imchipwood/dumbpad/case/case v2/img/1.jpg

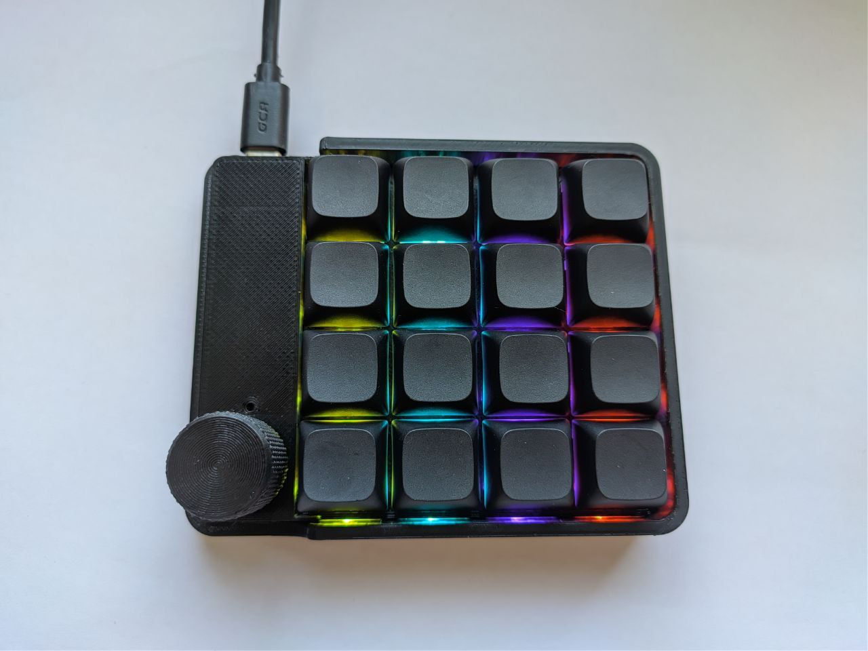
case/case v2/img/1.jpg
