imchipwood/dumbpad/case/case v2/img/2.jpg

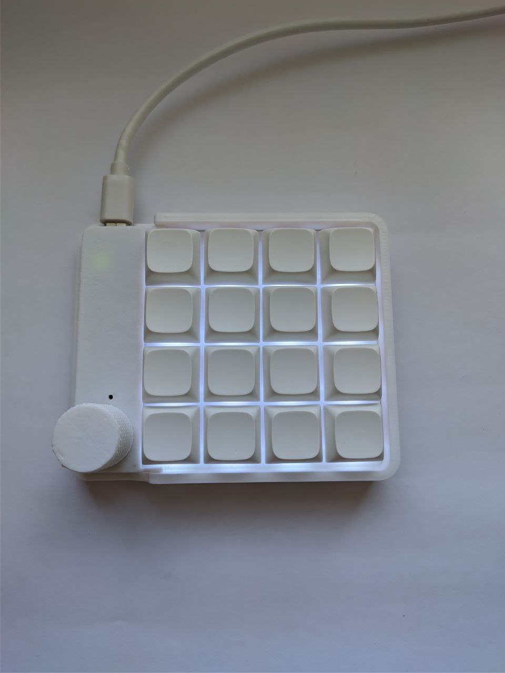
case/case v2/img/2.jpg
