imchipwood/dumbpad/case/case v2/img/3.jpg

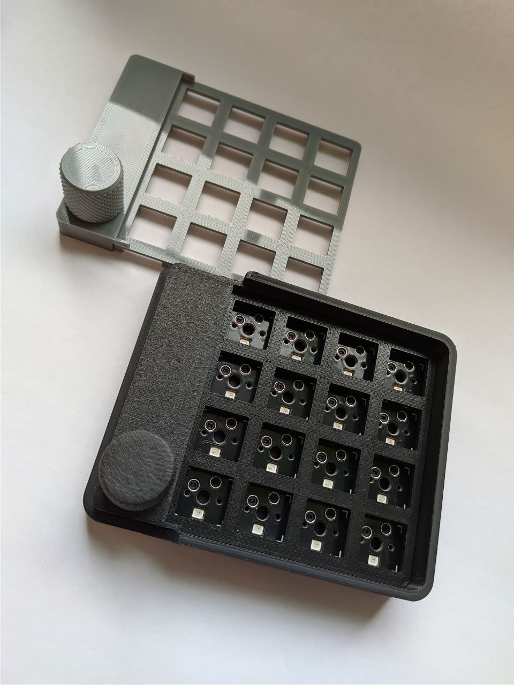
case/case v2/img/3.jpg
