imchipwood/dumbpad/case/case v2/img/4.jpg

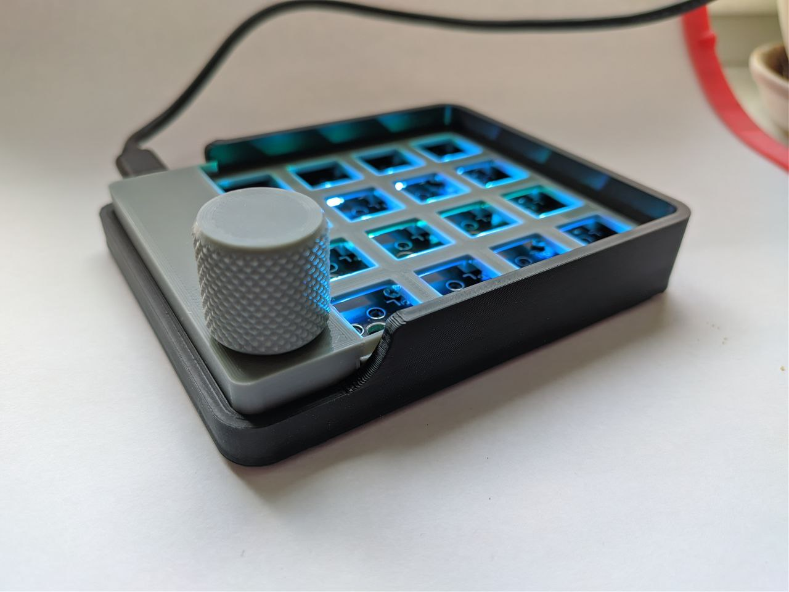
case/case v2/img/4.jpg
